DiegoLale/Laberinto_2016/piezas_laberinto/pared.stl

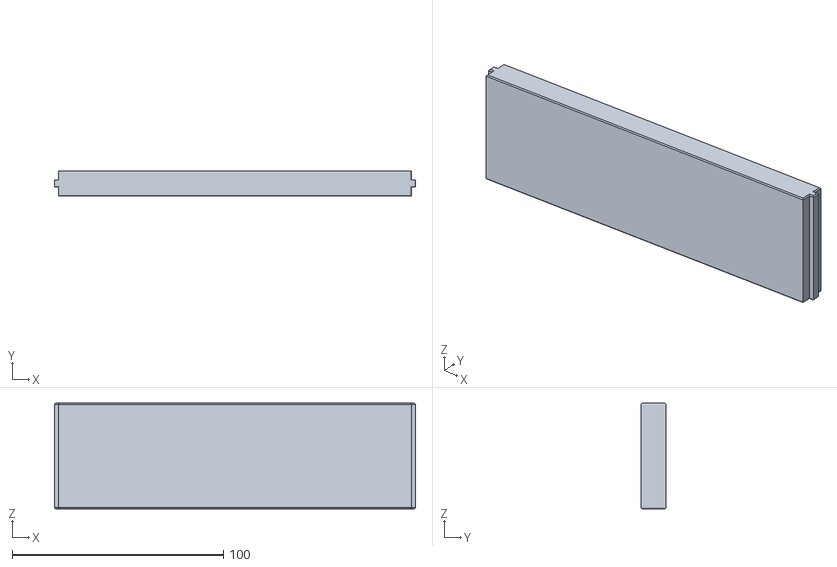
[picture p21: CAD file, 2017-10-20]
piezas_laberinto/pared.stl
171.0 x 12.0 x 50.0
