DiegoLale/Laberinto_2016/step/chasisInferior.step

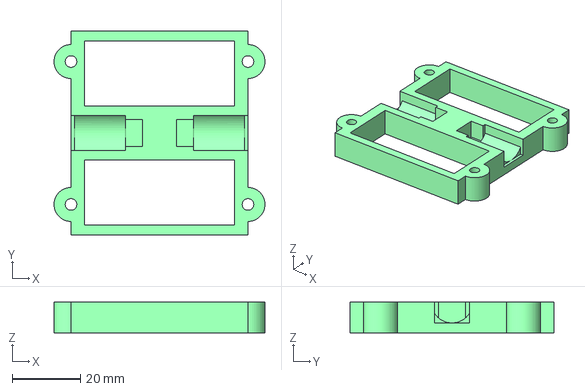
[picture p22: CAD file, 2016-10-15, an earlier design]
step/chasisInferior.step
62.0 x 60.0 x 9.00 mm
